Universidad-Cenfotec/Contraloria/Design/Caja_Camara_P1.stl

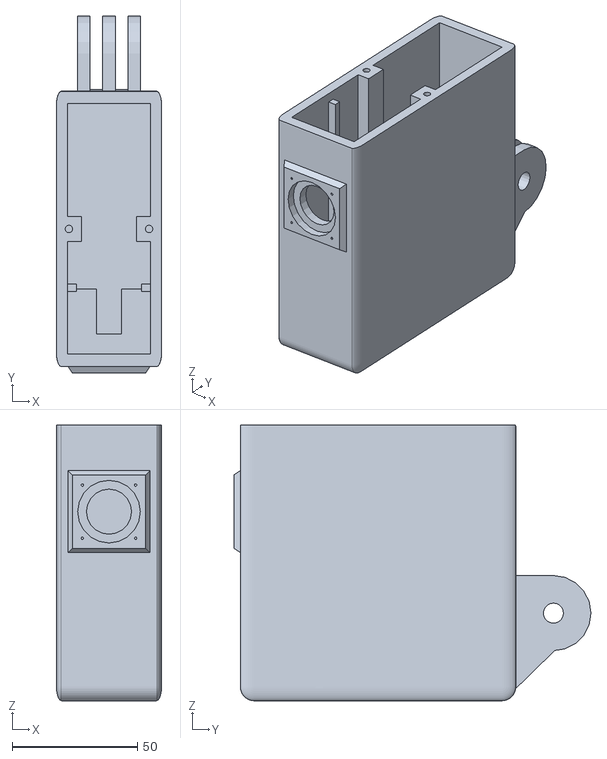
[picture p133: CAD file, 2024-04-08]
Design/Caja_Camara_P1.stl
42.0 x 142.5 x 110.0
