Universidad-Cenfotec/Contraloria/Design/Visor_Camara.stl

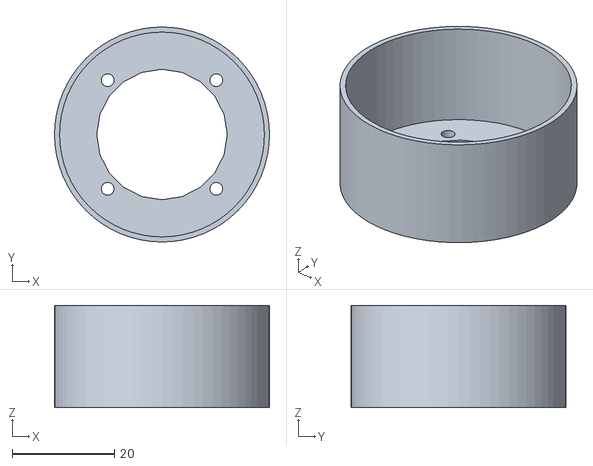
[picture p138: CAD file, 2024-04-08]
Design/Visor_Camara.stl
42.0 x 42.0 x 20.0
