Universidad-Cenfotec/Contraloria/placa_tpl/tpl-esp32/3dparts/jst-sh-smd-connectors-1.snapshot.4/SHR-xxV-S/SHR-03V-S.STEP

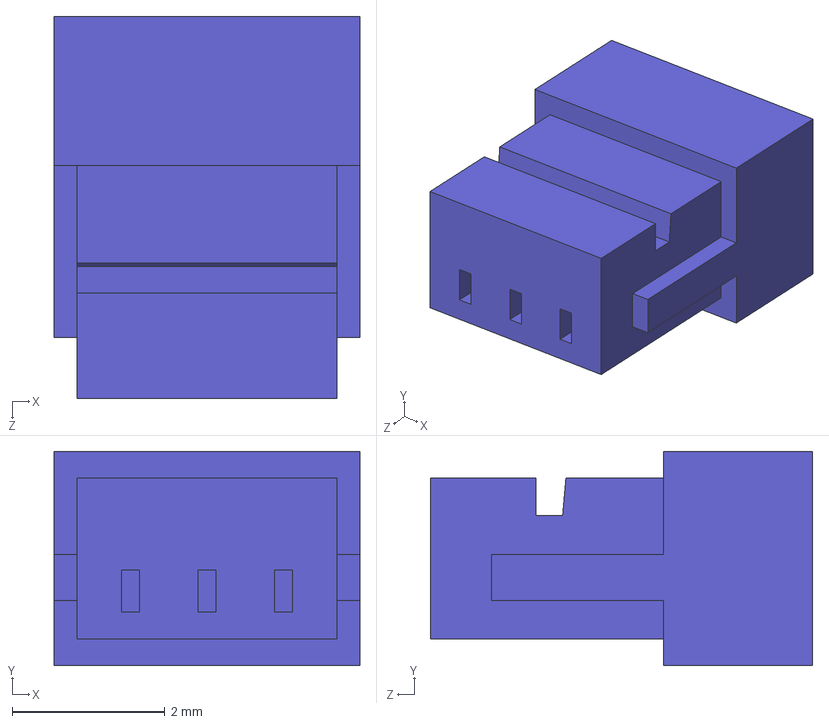
[picture p141: CAD file, 2024-04-12]
placa_tpl/tpl-esp32/3dparts/jst-sh-smd-connectors-1.snapshot.4/SHR-xxV-S/SHR-03V-S.STEP
4.00 x 2.80 x 5.00 mm
