Universidad-Cenfotec/Contraloria/placa_tpl/tpl-esp32/3dparts/jst-sh-smd-connectors-1.snapshot.4/SMxxB-SRSS-TB/SM20B-SRSS-TB.STEP

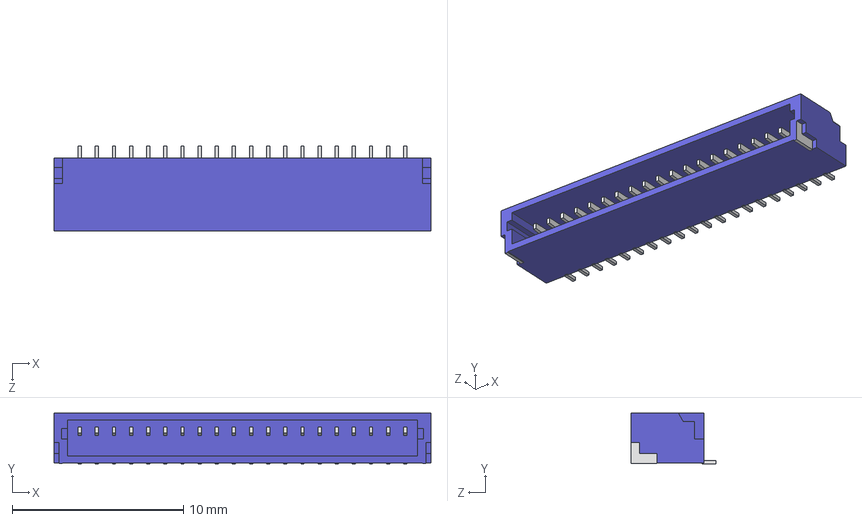
[picture p142: CAD file, 2024-04-12]
placa_tpl/tpl-esp32/3dparts/jst-sh-smd-connectors-1.snapshot.4/SMxxB-SRSS-TB/SM20B-SRSS-TB.STEP
22.0 x 2.96 x 4.95 mm
