Universidad-Cenfotec/Contraloria/Design/Union_Camara_Poste.stl

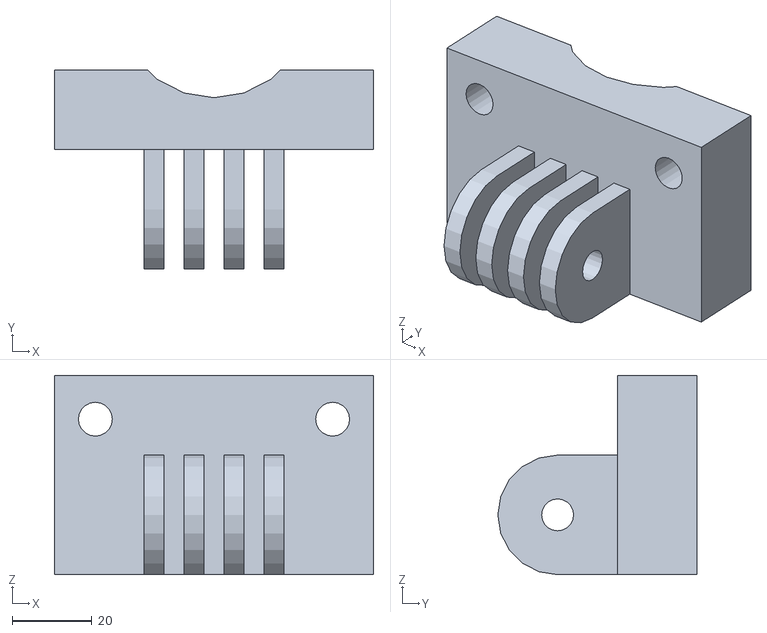
[picture p143: CAD file, 2024-04-08]
Design/Union_Camara_Poste.stl
80.0 x 50.0 x 50.0
