Universidad-Cenfotec/Contraloria/placa_tpl/tpl-esp32/3dparts/jst-sh-smd-connectors-1.snapshot.4/SHR-xxV-S-B/SHR-13V-S-B.STEP

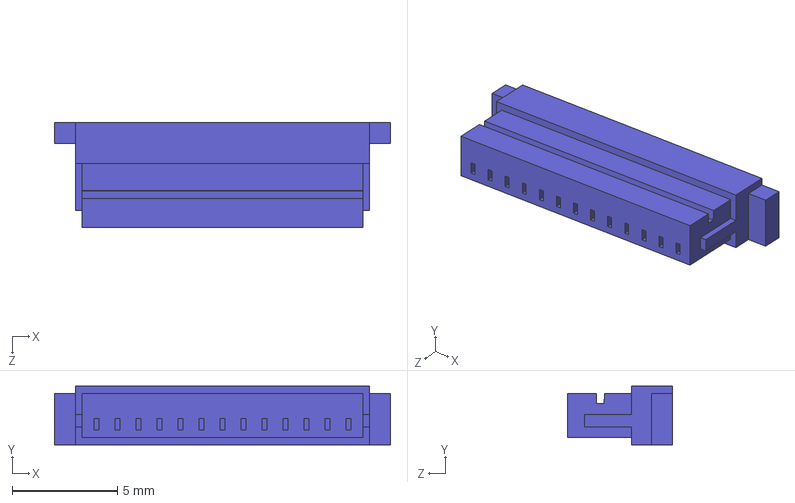
[picture p145: CAD file, 2024-04-12]
placa_tpl/tpl-esp32/3dparts/jst-sh-smd-connectors-1.snapshot.4/SHR-xxV-S-B/SHR-13V-S-B.STEP
16.0 x 2.80 x 5.00 mm
