Universidad-Cenfotec/Contraloria/placa_tpl/tpl-esp32/3dparts/jst-sh-smd-connectors-1.snapshot.4/SMxxB-SRSS-TB/SM06B-SRSS-TB.STEP

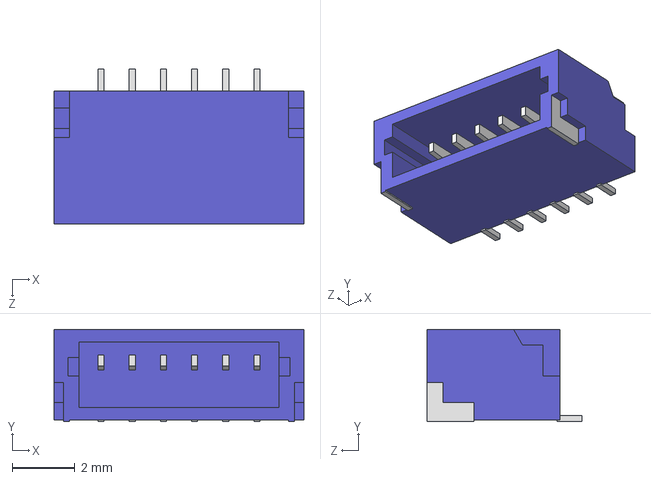
[picture p147: CAD file, 2024-04-12]
placa_tpl/tpl-esp32/3dparts/jst-sh-smd-connectors-1.snapshot.4/SMxxB-SRSS-TB/SM06B-SRSS-TB.STEP
8.00 x 2.96 x 4.95 mm
