Universidad-Cenfotec/Contraloria/placa_tpl/tpl-esp32/3dparts/jst-sh-smd-connectors-1.snapshot.4/BMxxB-SRSR-TB/BM07B-SRSS-TB.STEP

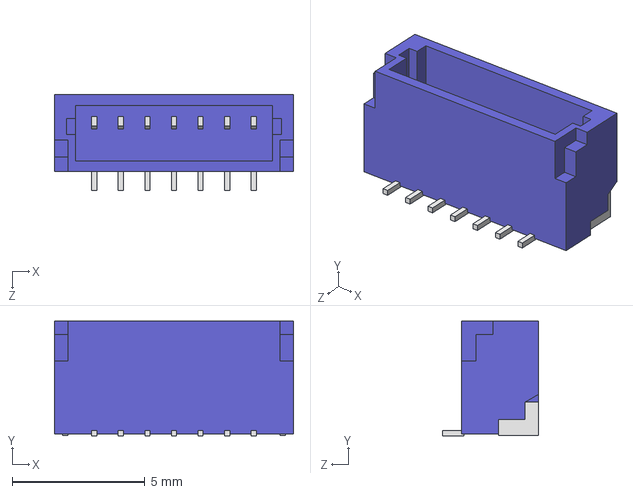
[picture p148: CAD file, 2024-04-12]
placa_tpl/tpl-esp32/3dparts/jst-sh-smd-connectors-1.snapshot.4/BMxxB-SRSR-TB/BM07B-SRSS-TB.STEP
9.00 x 4.32 x 3.60 mm
