Universidad-Cenfotec/Contraloria/placa_tpl/tpl-esp32/3dparts/jst-sh-smd-connectors-1.snapshot.4/SMxxB-SRSS-TB/SM02B-SRSS-TB.STEP

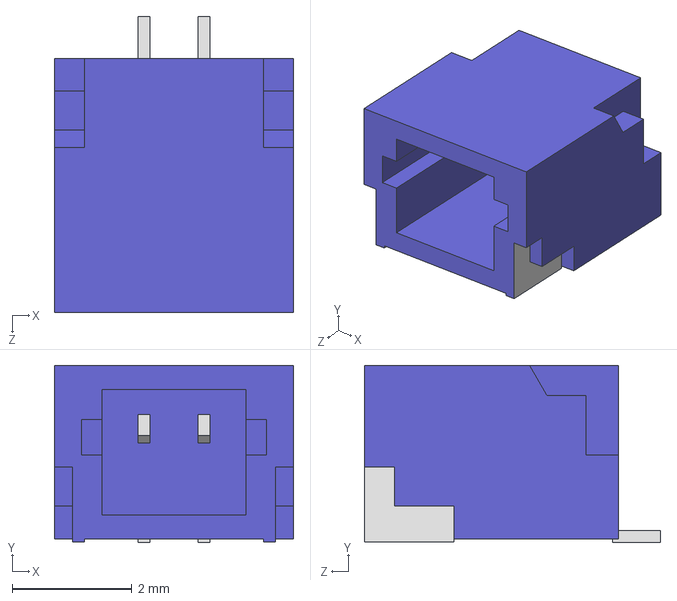
[picture p155: CAD file, 2024-04-12]
placa_tpl/tpl-esp32/3dparts/jst-sh-smd-connectors-1.snapshot.4/SMxxB-SRSS-TB/SM02B-SRSS-TB.STEP
4.00 x 2.96 x 4.95 mm
